vojtamolda/usb-board/prototype/atmega168/atmega168.sch

## EAGLE design prototype/atmega168/atmega168.sch (2015-12-05)

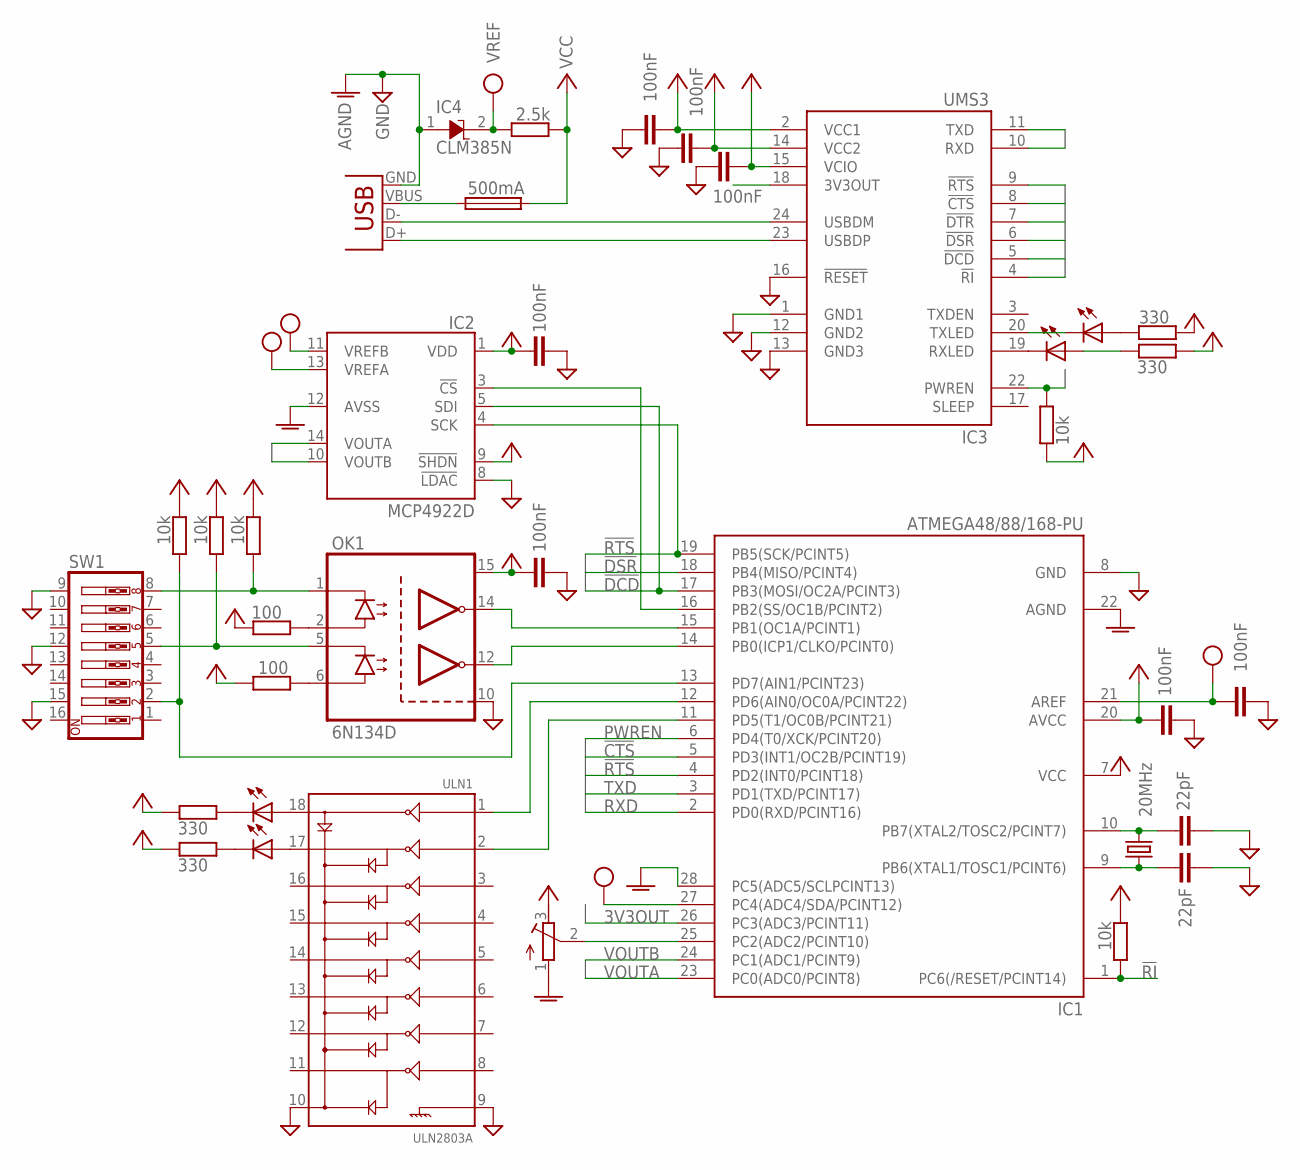
[picture p43: schematic atmega168.sch]

Parts:
C1, C4, C5, C6, C7, C8, C9: 100nF; C025-025X050
C2, C3: 22pF; C025-025X050
F1: 500mA; GSH15
IC1: ATMEGA48/88/168-PU; DIL28-3
IC2: MCP4922D; DIL-14
IC3: UMS3; DIL-24
IC4: CLM385N; TO-92
OK1: 6N134D; DIL-16
Q1: 20MHz; HC49/S
R1, R2, R12, R13: 330; 0411/12
R3: R-TRIMM4G/J; RTRIM4G/J
R4: 2.5k; 0411/12
R5, R6, R9, R10, R11: 10k; 0411/12
R7, R8: 100; 0411/12
RLED, RLED1, RLED2: LED3MM
SW1: SW_DIP-8; DIPSWITCH-08
TLED: LED3MM
ULN1: ULN2803A; DIL18
X1: USB-PTH; USB-B-PTH

Connections:
3V3OUT: IC1.26 (PC3(ADC3/PCINT11)), IC3.18 (3V3OUT)
!CTS: IC1.5 (PD3(INT1/OC2B/PCINT19)), IC3.8 (!CTS)
!DCD: IC1.17 (PB3(MOSI/OC2A/PCINT3)), IC2.5 (SDI), IC3.5 (!DCD)
!DSR: IC1.18 (PB4(MISO/PCINT4)), IC3.6 (!DSR)
!DTR: IC3.7 (!DTR)
!RI: IC1.1 (PC6(/RESET/PCINT14)), R5.2
!RTS: IC1.4 (PD2(INT0/PCINT18)), IC1.19 (PB5(SCK/PCINT5)), IC2.4 (SCK), IC3.9 (!RTS)
AGND: IC1.22 (AGND), IC1.28 (PC5(ADC5/SCLPCINT13)), IC2.12 (AVSS), IC4.1 (ANO), R3.1 (E), X1.GND
GND: C1.1, C2.1, C3.1, C4.1, C5.2, C6.2, C7.2, C8.2, C9.1, IC1.8 (GND), IC2.8 (!LDAC), IC3.1 (GND1), IC3.12 (GND2), IC3.13 (GND3), IC3.16 (!RESET), OK1.10 (GND), SW1.9, SW1.12, SW1.15, ULN1.9, ULN1.10
unnamed: IC3.24 (USBDM), X1.D-
unnamed: IC3.23 (USBDP), X1.D+
unnamed: IC3.19 (RXLED), RLED.K (C)
unnamed: F1.2, X1.VBUS
unnamed: IC3.20 (TXLED), TLED.K (C)
unnamed: R1.1, RLED.A
unnamed: R2.1, TLED.A
unnamed: IC1.12 (PD6(AIN0/OC0A/PCINT22)), ULN1.1
unnamed: IC1.11 (PD5(T1/OC0B/PCINT21)), ULN1.2
unnamed: IC1.15 (PB1(OC1A/PCINT1)), OK1.14 (VOUT1)
unnamed: IC1.14 (PB0(ICP1/CLKO/PCINT0)), OK1.12 (VOUT2)
unnamed: IC1.13 (PD7(AIN1/PCINT23)), R9.2, SW1.2
unnamed: OK1.2 (ANODE1), R7.2
unnamed: OK1.6 (ANODE2), R8.1
unnamed: C3.2, IC1.9 (PB6(XTAL1/TOSC1/PCINT6)), Q1.1
unnamed: C2.2, IC1.10 (PB7(XTAL2/TOSC2/PCINT7)), Q1.2
unnamed: OK1.5 (KATHODE2), R11.2, SW1.5
unnamed: IC1.16 (PB2(SS/OC1B/PCINT2)), IC2.3 (!CS)
unnamed: OK1.1 (KATHODE1), R10.2, SW1.8
unnamed: IC1.25 (PC2(ADC2/PCINT10)), R3.2 (S)
unnamed: RLED2.A, ULN1.18
unnamed: RLED1.A, ULN1.17
unnamed: R12.2, RLED1.K (C)
unnamed: R13.2, RLED2.K (C)
PWREN: IC1.6 (PD4(T0/XCK/PCINT20)), IC3.22 (PWREN), R6.2
RXD: IC1.2 (PD0(RXD/PCINT16)), IC3.10 (RXD)
TXD: IC1.3 (PD1(TXD/PCINT17)), IC3.11 (TXD)
VCC: C1.2, C4.2, C5.1, C6.1, C7.1, C8.1, C9.2, F1.1, IC1.7 (VCC), IC1.20 (AVCC), IC1.21 (AREF), IC1.27 (PC4(ADC4/SDA/PCINT12)), IC2.1 (VDD), IC2.9 (!SHDN), IC2.11 (VREFB), IC2.13 (VREFA), IC3.2 (VCC1), IC3.14 (VCC2), IC3.15 (VCIO), IC4.2 (CAT), OK1.15 (VCC), R1.2, R2.2, R3.3 (A), R4.1, R4.2, R5.1, R6.1, R7.1, R8.2, R9.1, R10.1, R11.1, R12.1, R13.1
VOUTA: IC1.23 (PC0(ADC0/PCINT8)), IC2.14 (VOUTA)
VOUTB: IC1.24 (PC1(ADC1/PCINT9)), IC2.10 (VOUTB)
