vojtamolda/usb-board/prototype/bitbang/bitbang.sch

## EAGLE design prototype/bitbang/bitbang.sch (2015-12-05)

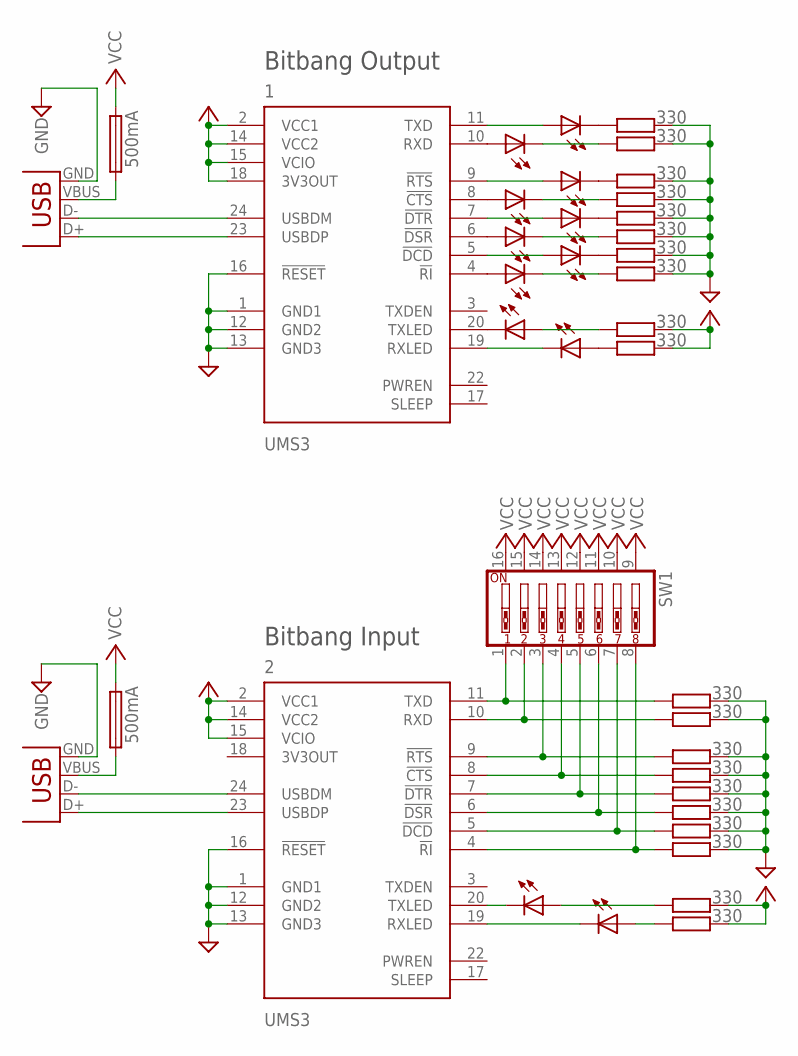
[picture p44: schematic bitbang.sch]

Parts:
1, 2: UMS3; DIL-24
F1, F2: 500mA; GSH15
LED1, LED2, LED3, LED4, LED5, LED6, LED7, LED8: LED3MM
R1, R2, R3, R4, R5, R6, R7, R8, R9, R10, R11, R12, R13, R14, R15, R16, R17, R18, R19, R20: 330; 0411/12
RLED, RLED1: LED3MM
SW1: SW_DIP-8; EDG-08
TLED, TLED1: LED3MM
X1, X2: USB-PTH; USB-B-PTH

Connections:
GND: 1.1 (GND1), 1.12 (GND2), 1.13 (GND3), 1.16 (!RESET), 2.1 (GND1), 2.12 (GND2), 2.13 (GND3), 2.16 (!RESET), R3.2, R4.2, R5.2, R6.2, R7.2, R8.2, R9.2, R10.2, R13.2, R14.2, R15.2, R16.2, R17.2, R18.2, R19.2, R20.2, X2.GND
unnamed: 1.24 (USBDM), X1.D-
unnamed: 1.23 (USBDP), X1.D+
unnamed: 1.11 (TXD), LED1.A
unnamed: 1.9 (!RTS), LED3.A
unnamed: 1.20 (TXLED), TLED.K (C)
unnamed: R1.1, RLED.A
unnamed: 1.19 (RXLED), RLED.K (C)
unnamed: R2.1, TLED.A
unnamed: 1.7 (!DTR), LED5.A
unnamed: 1.5 (!DCD), LED7.A
unnamed: LED1.K (C), R3.1
unnamed: LED2.K (C), R4.1
unnamed: LED3.K (C), R5.1
unnamed: 1.10 (RXD), LED2.A
unnamed: 1.8 (!CTS), LED4.A
unnamed: LED4.K (C), R6.1
unnamed: LED5.K (C), R7.1
unnamed: LED7.K (C), R9.1
unnamed: LED8.K (C), R10.1
unnamed: 1.4 (!RI), LED8.A
unnamed: 1.6 (!DSR), LED6.A
unnamed: LED6.K (C), R8.1
unnamed: 2.24 (USBDM), X2.D-
unnamed: 2.23 (USBDP), X2.D+
unnamed: R11.1, RLED1.A
unnamed: 2.19 (RXLED), RLED1.K (C)
unnamed: R12.1, TLED1.A
unnamed: 2.20 (TXLED), TLED1.K (C)
unnamed: 2.11 (TXD), R13.1, SW1.1
unnamed: 2.10 (RXD), R14.1, SW1.2
unnamed: 2.9 (!RTS), R15.1, SW1.3
unnamed: 2.8 (!CTS), R16.1, SW1.4
unnamed: 2.7 (!DTR), R17.1, SW1.5
unnamed: 2.6 (!DSR), R18.1, SW1.6
unnamed: 2.5 (!DCD), R19.1, SW1.7
unnamed: 2.4 (!RI), R20.1, SW1.8
unnamed: F2.2, X2.VBUS
unnamed: R11.2, R12.2
VCC: 1.2 (VCC1), 1.14 (VCC2), 1.15 (VCIO), 1.18 (3V3OUT), 2.2 (VCC1), 2.14 (VCC2), 2.15 (VCIO), F1.1, F2.1, R1.2, R2.2, SW1.9, SW1.10, SW1.11, SW1.12, SW1.13, SW1.14, SW1.15, SW1.16

Notes on the sheet:
Bitbang Input
Bitbang Output
