vojtamolda/usb-board/prototype/discover/discover.sch

## EAGLE design prototype/discover/discover.sch (2015-12-05)

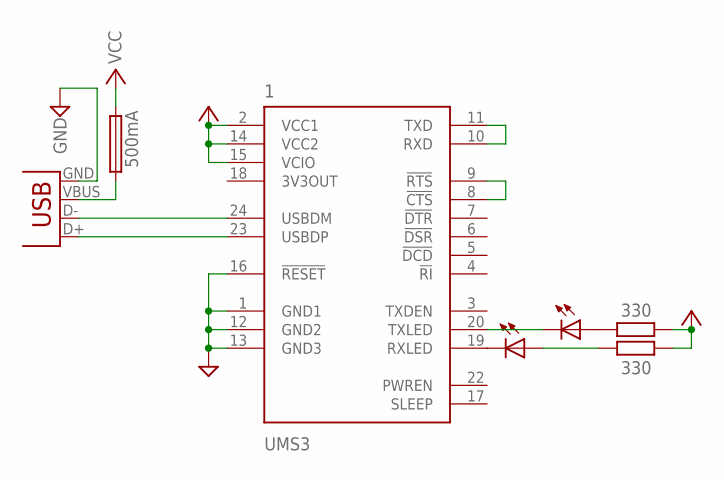
[picture p45: schematic discover.sch]

Parts:
1: UMS3; DIL-24
F1: 500mA; GSH15
R1, R2: 330; 0411/12
RLED: LED3MM
TLED: LED3MM
X1: USB-PTH; USB-B-PTH

Connections:
GND: 1.1 (GND1), 1.12 (GND2), 1.13 (GND3), 1.16 (!RESET), X1.GND
unnamed: 1.24 (USBDM), X1.D-
unnamed: 1.23 (USBDP), X1.D+
unnamed: 1.10 (RXD), 1.11 (TXD)
unnamed: F1.2, X1.VBUS
unnamed: 1.20 (TXLED), TLED.K (C)
unnamed: R1.1, RLED.A
unnamed: 1.19 (RXLED), RLED.K (C)
unnamed: R2.1, TLED.A
unnamed: 1.8 (!CTS), 1.9 (!RTS)
VCC: 1.2 (VCC1), 1.14 (VCC2), 1.15 (VCIO), F1.1, R1.2, R2.2
